preparedinstruments/bechamel/verilog/SRAM FPGA 800 x 600 at 50MHz/bechamel_VGA_ROM.v

module vga_sync_test(
    input wire clk_in,
	input wire [8:0] key,
	input wire rpi_vsync,
	input wire rpi_hsync,
	input wire analog_in,
	inout pot_in,
	output [3:0] hdmi_p,
	output [3:0] hdmi_n,
     output reg [3:0] r_out,
     output reg [3:0] b_out,
     output reg [3:0] g_out,
     output wire h_sync,
     output wire v_sync,
     output wire red_led,
	output wire green_led
  );
  
  

//160x120
reg [0:19199] heart =

{
160'b0000000000000000000000000000000000000011111111111111111111111111111111111101111100001111110000011111111111111111111111111111111111111111111111111111111111111111,
160'b0000000000000000000000000000000000000011111111111111111111111111111111111100000111111111111111000011100111111111111111111111111111111111111111111111111111111111,
160'b0000000000000000000000000000000000000011111111111111111111111111111111111111111111111111111111111111101111111111111111111111111111111111111111111111111111111111,
160'b0000000000000000000000000000000000110000110001111111111111111111111111111111111111111111111111111111111111111111111111111111111111111111111111111111111111111111,
160'b0000000000000000000000000000000000110000011011111111111111111111111111111111111111111111111111111111111111110111111111111111111111111111111111111111111111111111,
160'b0000000000000000000000000000000000110000011111111111111111111111111111111111111111111111111111111111111111100111111111111111111111111111111111111111111111111111,
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


always @(posedge half_sec_pulse) begin

        data_out <= data;
        addr <= addr + 1;
        if(addr == 29)
            addr <= 0;

end

// FOR AUDIO IN INTERACTION
assign red_led = analog_in;
assign green_led = analog_in;  

// FOR KEY INTERACTION key[8:0]

// FOR POT INTERACTION

reg [15:0] adc_count= 0; //16 bits to count how long it's taking to charge. 32,768 is the max value. 1 extra MSB bit for just discharging the cap.
reg [14:0] pot_value= 0; //to store cap charge time value
reg [14:0] final_pot_value= 0;

wire adc_in;
reg adc_sample = 1; //first time through we want to sample the cap value

wire adc;


assign pot_in = (adc_sample) ? 1'bZ : 1'b0;
assign adc_in = pot_in;

// for a 25MHz clock we divide 100MHz by 4
reg [1:0] clk_div = 0;

always @(posedge clk_in)
begin
     clk_div <= clk_div + 1;
end


always @(posedge clk_div[1]) begin //25MHz clock
	
	adc_count <= adc_count + 1; // start counting

		if(adc_count>=16'b1000000000000000 )begin // once we have rolled over 15 bit counter...

			adc_sample <= 1'b0; // ...discharge cap for a while to restart the process.

		end

		else begin
			
			adc_sample<=1'b1; //put cap pin in high 'Z'

			if(adc_in==1'b1) begin // if cap charged...

				pot_value[14:0]<=adc_count[14:0]; //store this value in pot 

				
			end

		end

end


// FOR SOUND INTERACTION 

// FOR AUDIO IN INTERACTION

//Check if we can create RGB colors
always @(posedge clk_in) begin
			
	if (display_en) begin
	
		//divide hc (once in visible area) by 8, divide vc (once in visible area) by 8 and multiply by the row width
		pixel = heart[(((h_count)>>(~key[7:4]))+(((v_count)>>(~key[3:0]))*160))];
			
				if (pixel == 1'b1) begin
				//yellow
					r_out <= key[2:0];
					g_out <= key[5:3];
					b_out <= key[8:6];	
				end
				else begin
					r_out <= key[8:6];
					g_out <= key[5:3];
					b_out <= key[2:0];
				end
	end

	else begin
	
		r_out <= 3'b000;
	    g_out <= 3'b000;
		b_out <= 3'b000;	
			
	end	

end
vga_sync vga_s(
      .clk_in(clk_div[0]),         //50MHz
      .h_sync(h_sync),
      .v_sync(v_sync),
      .h_count(h_count),
      .v_count(v_count),
      .display_en(display_en) // '1' => pixel region
      );

endmodule
